Sappling-Chores/Cyprus/Assets/Edit_Gallery/Edit2.png

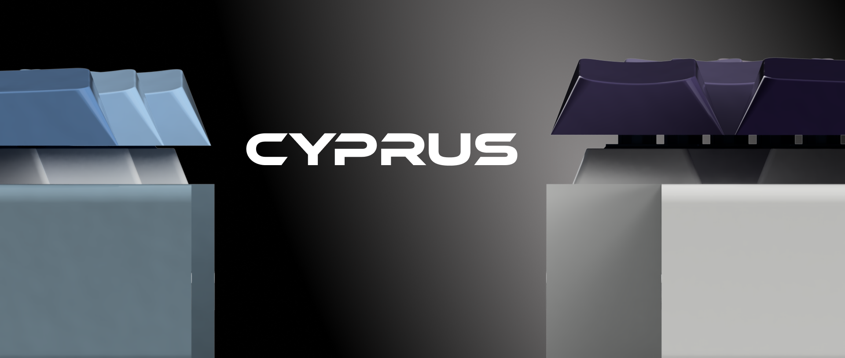
Assets/Edit_Gallery/Edit2.png
