Sappling-Chores/Cyprus/Assets/Edit_Gallery/Edit3.png

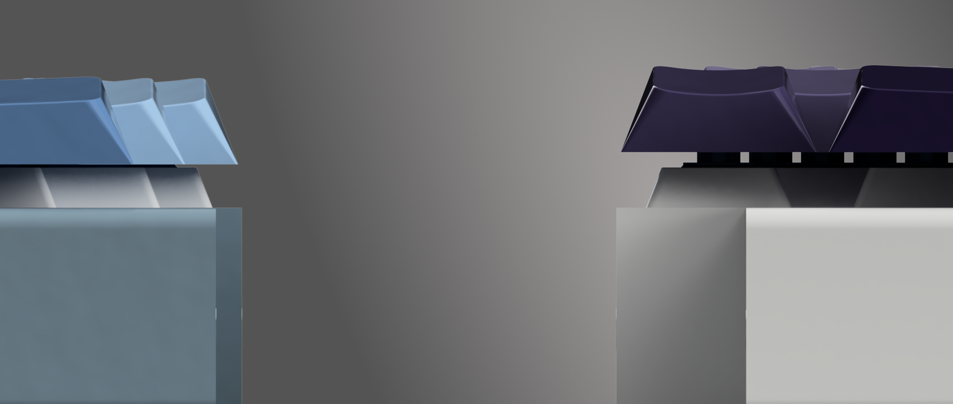
Assets/Edit_Gallery/Edit3.png
