Sappling-Chores/Cyprus/Assets/Edit_Gallery/Edit4.png

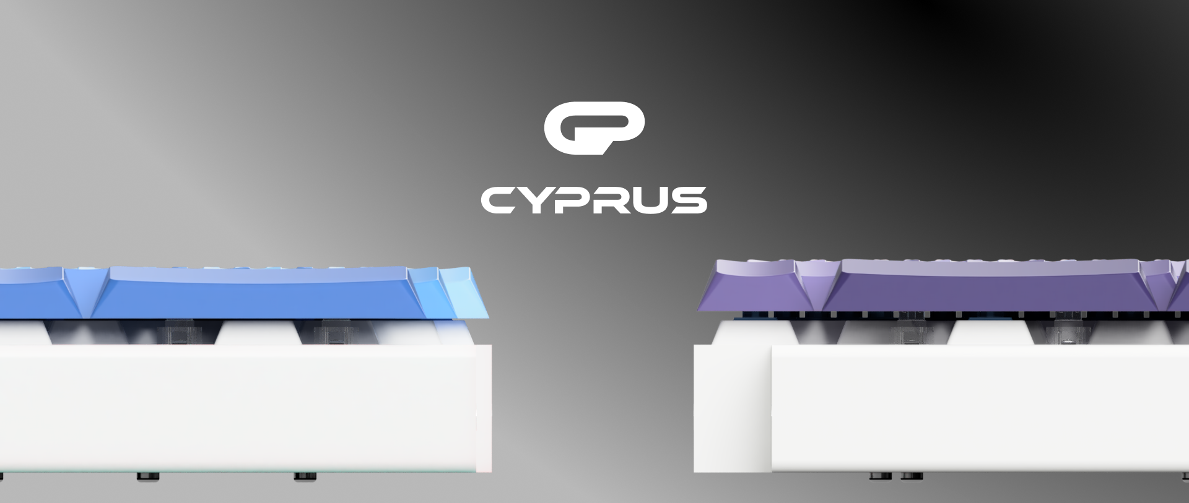
Assets/Edit_Gallery/Edit4.png
