Sappling-Chores/Cyprus/Assets/Edit_Gallery/Edit7 (2).png

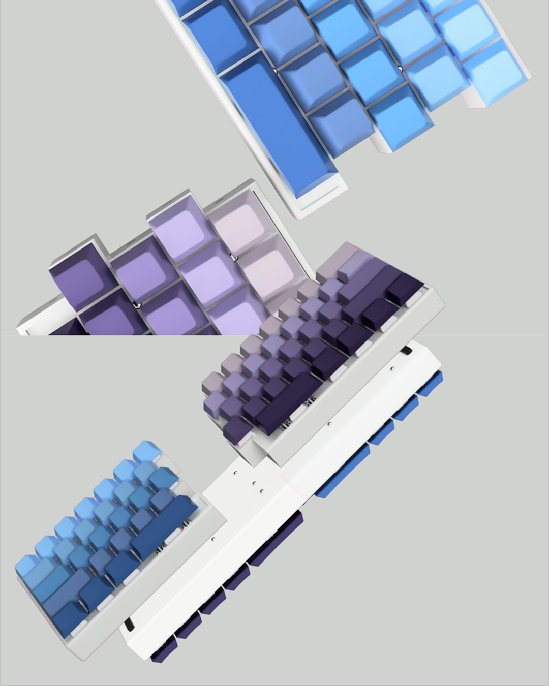
Assets/Edit_Gallery/Edit7 (2).png
