Sappling-Chores/Cyprus/Assets/Edit_Gallery/Edit9.png

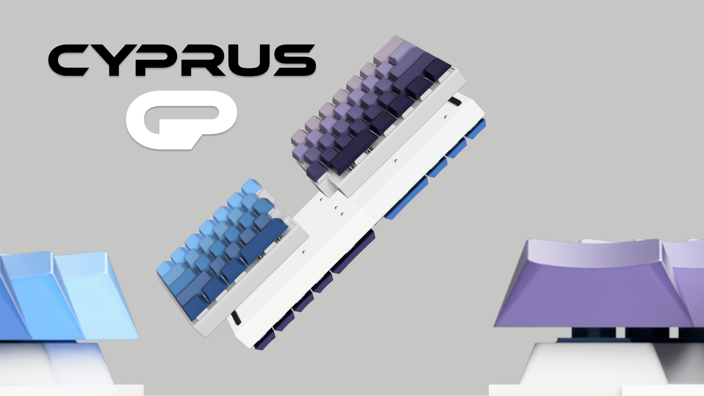
Assets/Edit_Gallery/Edit9.png
