Sappling-Chores/Cyprus/Assets/Edit_Gallery/Edit11.png

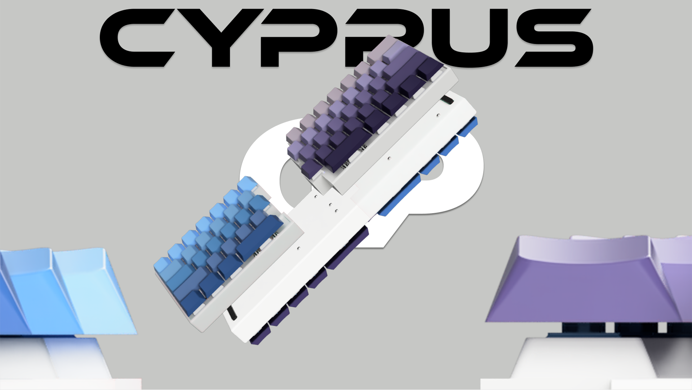
Assets/Edit_Gallery/Edit11.png
