Sappling-Chores/Cyprus/Assets/Edit_Gallery/Edit15.png

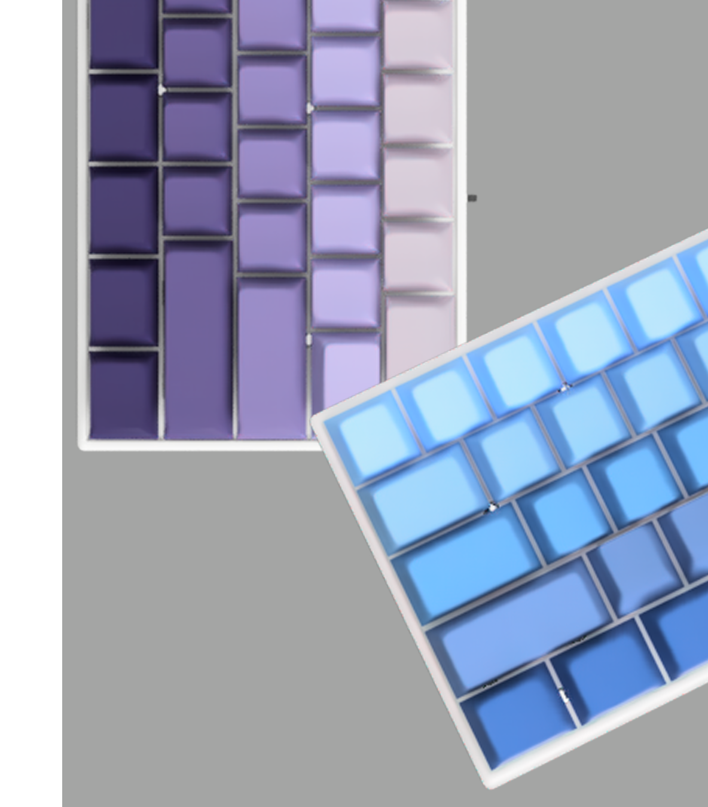
Assets/Edit_Gallery/Edit15.png
