Sappling-Chores/Cyprus/Assets/Edit_Gallery/Edit16.png

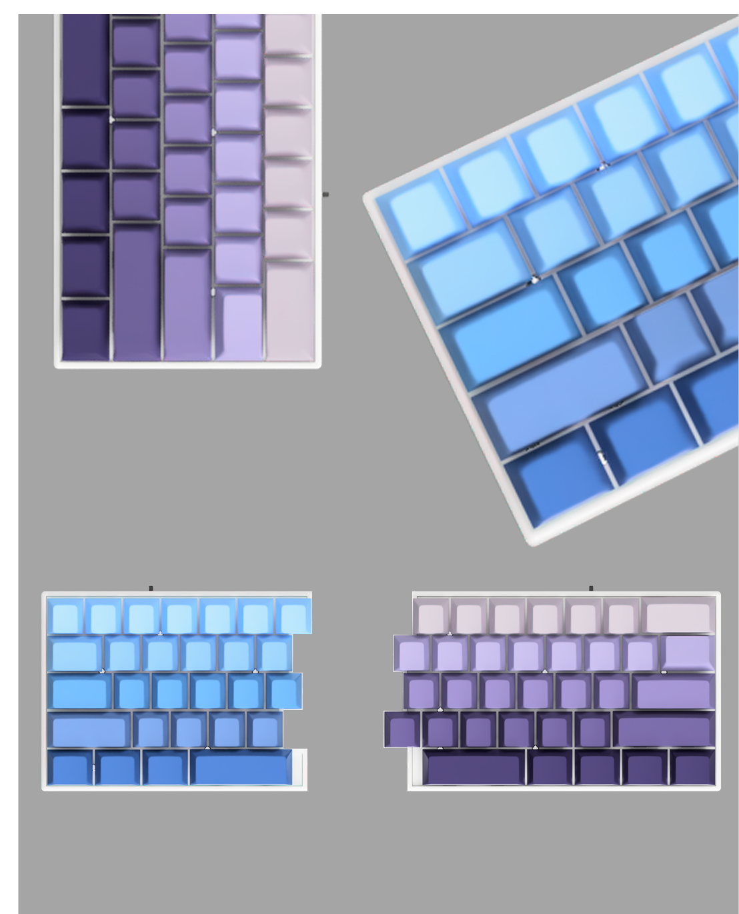
Assets/Edit_Gallery/Edit16.png
