Sappling-Chores/Cyprus/Assets/Edit_Gallery/Edit17.png

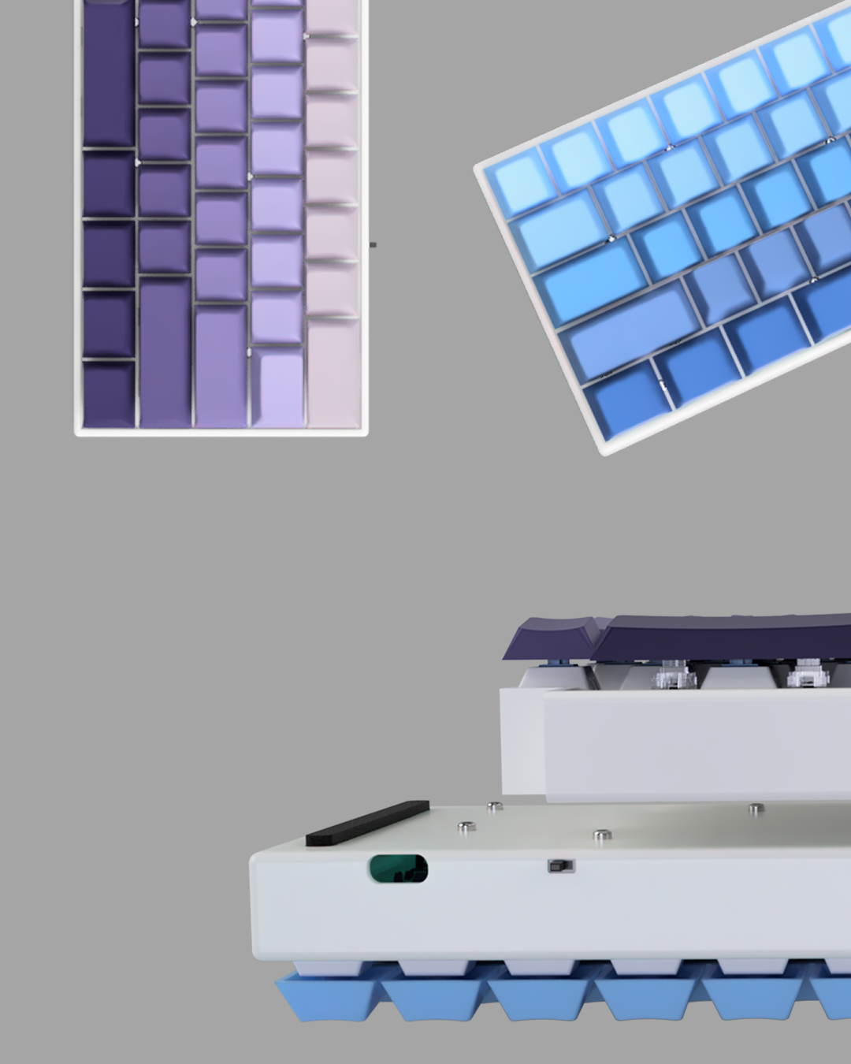
Assets/Edit_Gallery/Edit17.png
