Sappling-Chores/Cyprus/Assets/Edit_Gallery/Edit18.png

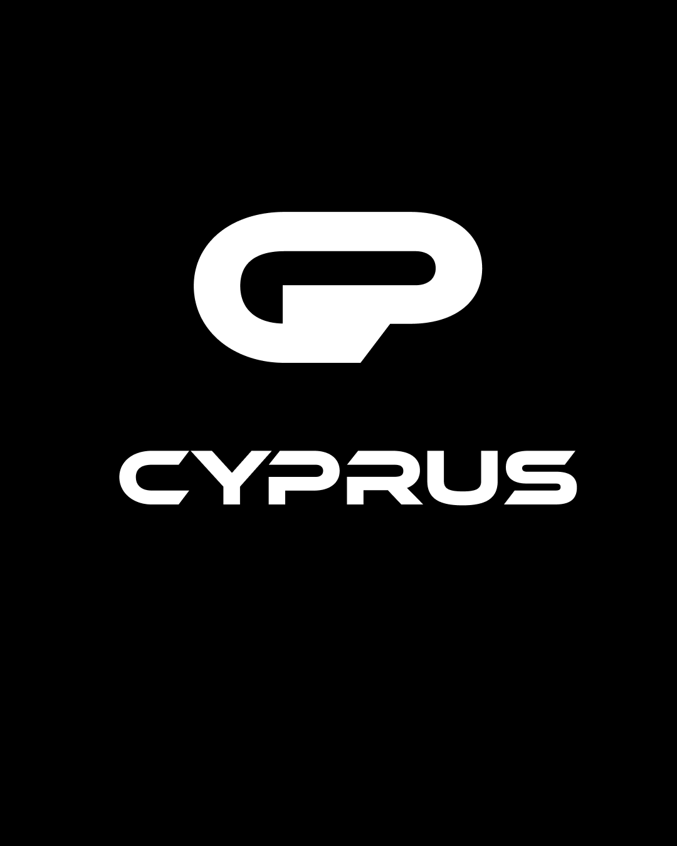
Assets/Edit_Gallery/Edit18.png
