Sappling-Chores/Cyprus/Assets/Edit_Gallery/Edit19.png

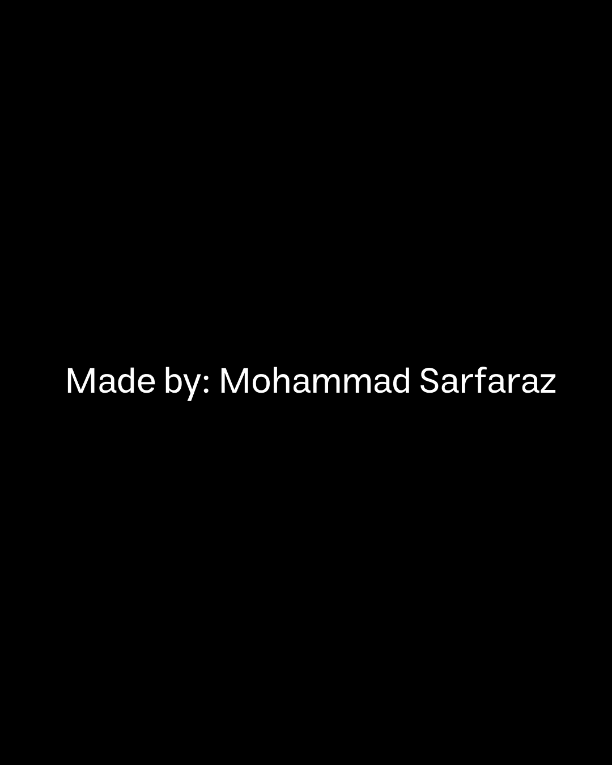
Assets/Edit_Gallery/Edit19.png
