Sappling-Chores/Cyprus/Assets/Render_Gallery/Render1.png

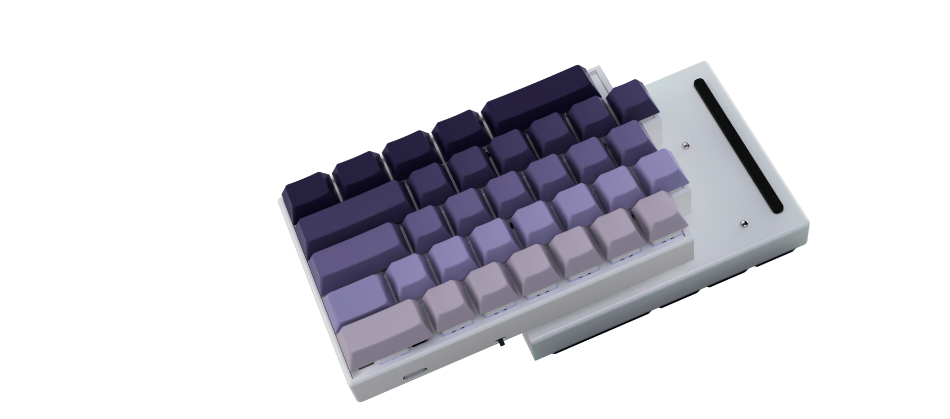
Assets/Render_Gallery/Render1.png
