Sappling-Chores/Cyprus/Assets/Render_Gallery/Render3.PNG

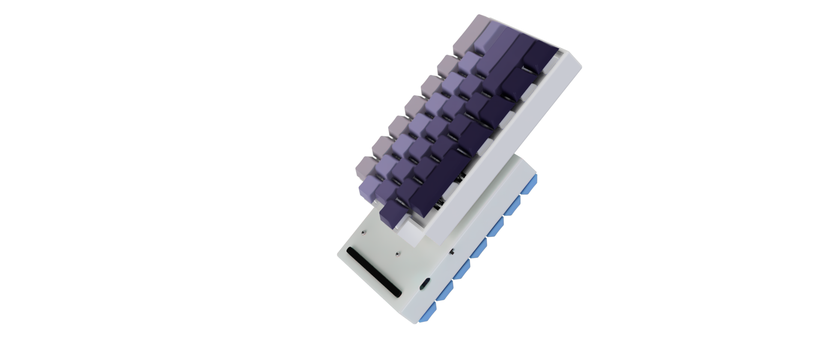
Assets/Render_Gallery/Render3.PNG
