Sappling-Chores/Cyprus/Assets/Render_Gallery/Render5.png

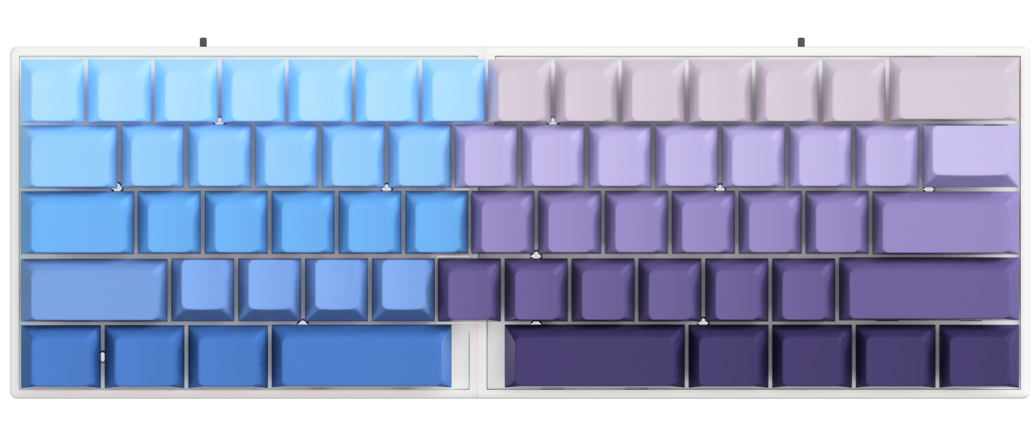
Assets/Render_Gallery/Render5.png
