Sappling-Chores/Cyprus/Assets/Render_Gallery/Render6.png

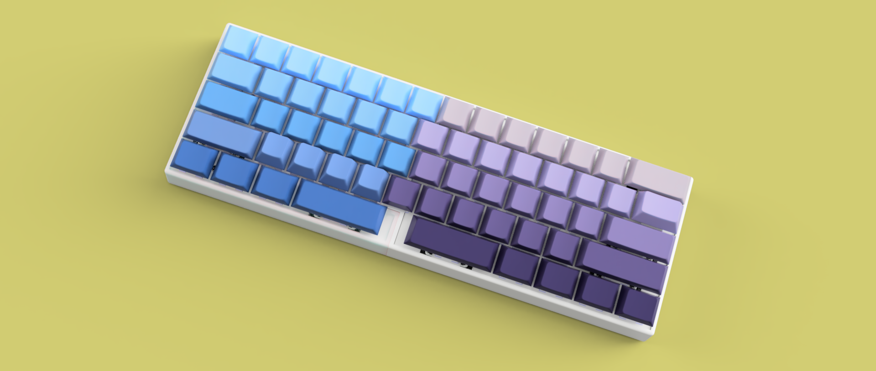
Assets/Render_Gallery/Render6.png
