Sappling-Chores/Cyprus/Assets/Render_Gallery/Render8.png

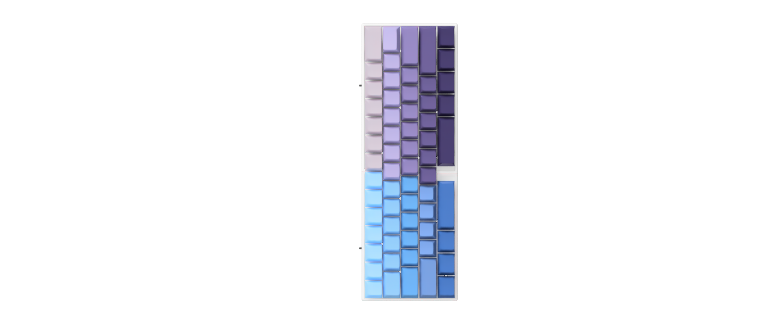
Assets/Render_Gallery/Render8.png
