Sappling-Chores/Cyprus/Assets/Render_Gallery/Render9.png

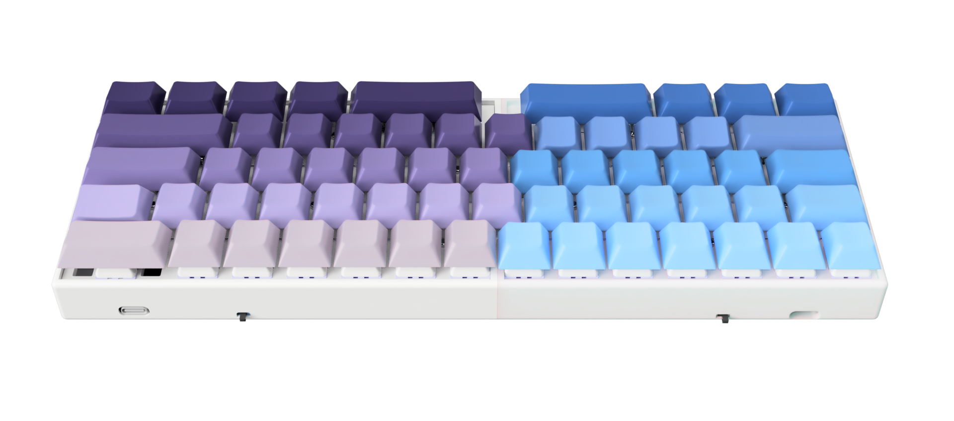
Assets/Render_Gallery/Render9.png
