Sappling-Chores/Cyprus/Assets/Render_Gallery/Render10.png

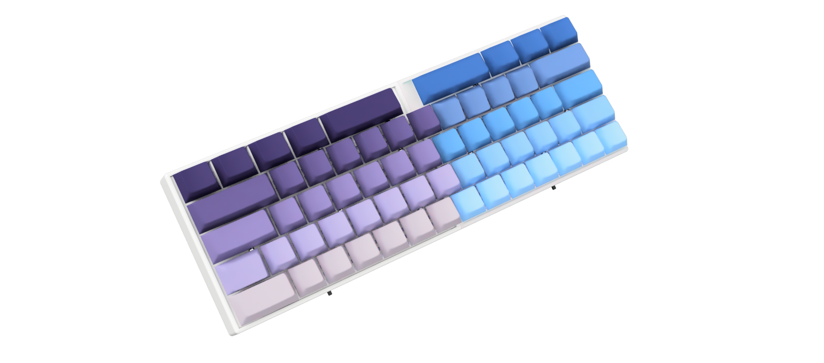
Assets/Render_Gallery/Render10.png
