Sappling-Chores/Cyprus/Assets/Render_Gallery/Render12.png

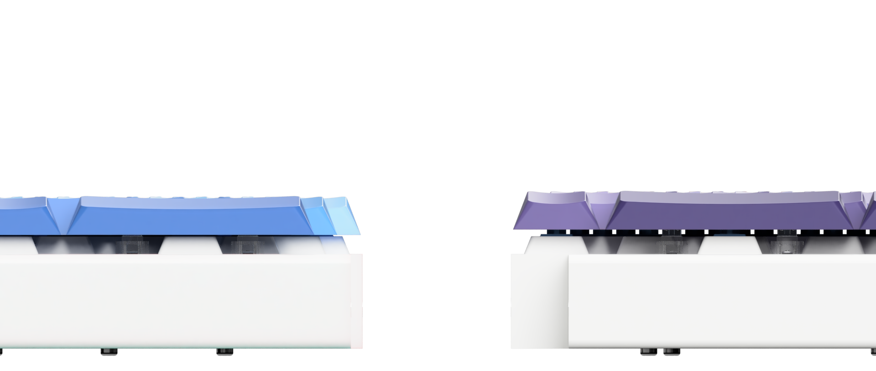
Assets/Render_Gallery/Render12.png
