Sappling-Chores/Cyprus/Assets/Render_Gallery/Render13.png

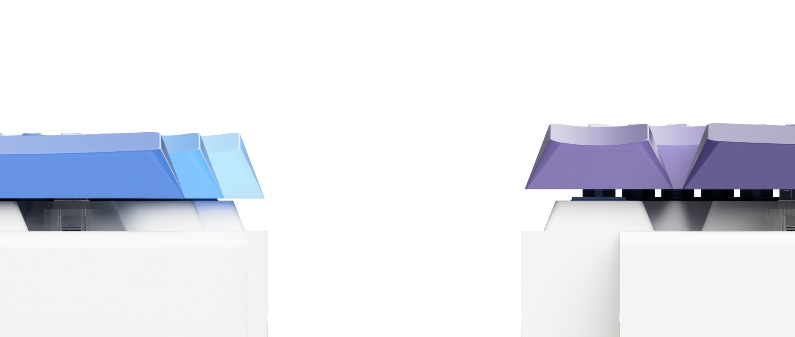
Assets/Render_Gallery/Render13.png
