Sappling-Chores/Cyprus/Assets/Render_Gallery/Render14.png

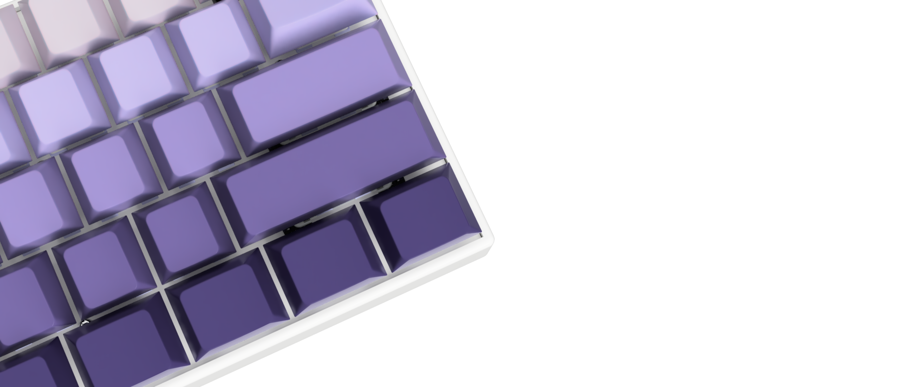
Assets/Render_Gallery/Render14.png
