Sappling-Chores/Cyprus/Assets/Render_Gallery/Render15.png

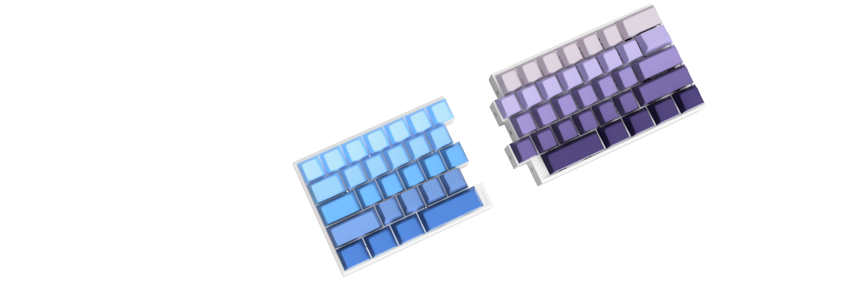
Assets/Render_Gallery/Render15.png
