Sappling-Chores/Cyprus/Assets/Render_Gallery/Render16.png

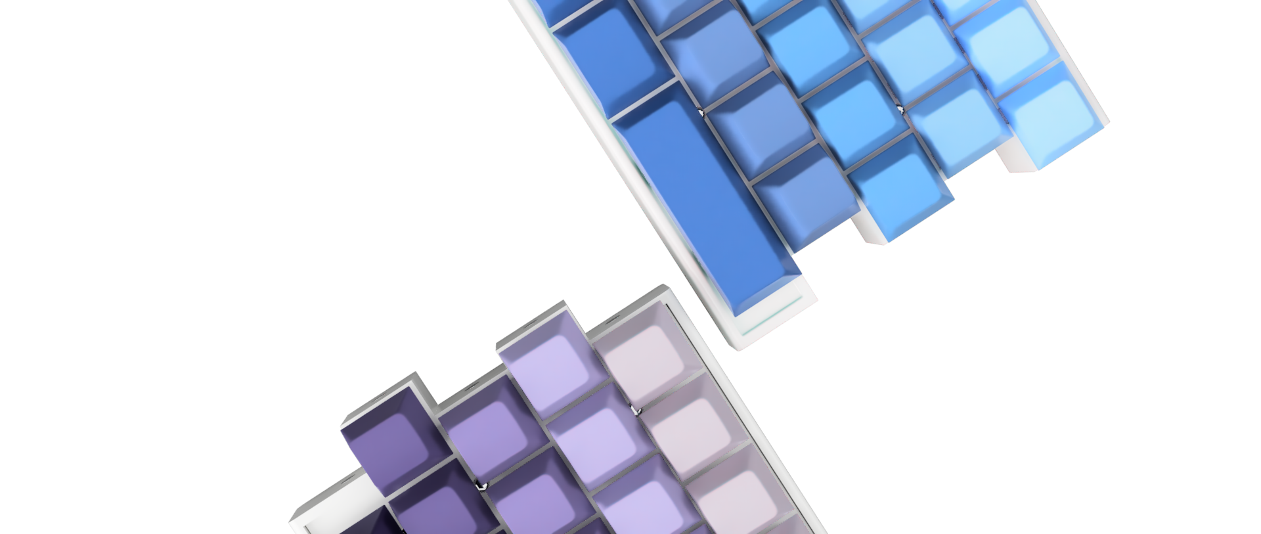
Assets/Render_Gallery/Render16.png
