Sappling-Chores/Cyprus/Assets/Render_Gallery/Render17.png

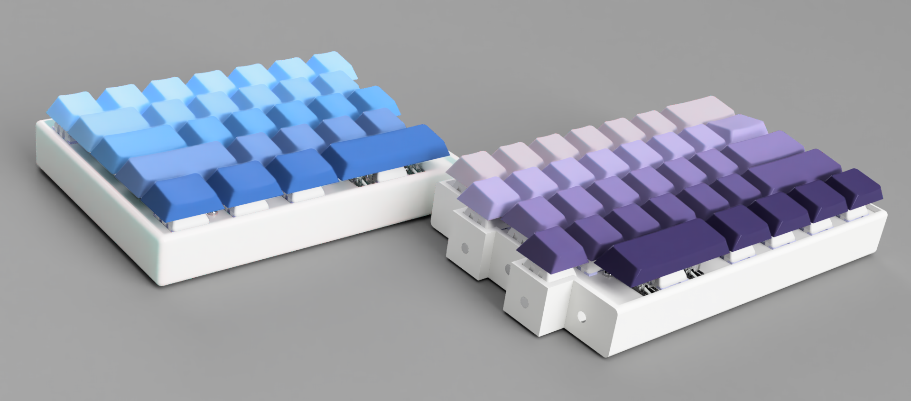
Assets/Render_Gallery/Render17.png
