Sappling-Chores/Cyprus/Assets/Render_Gallery/Render21.png

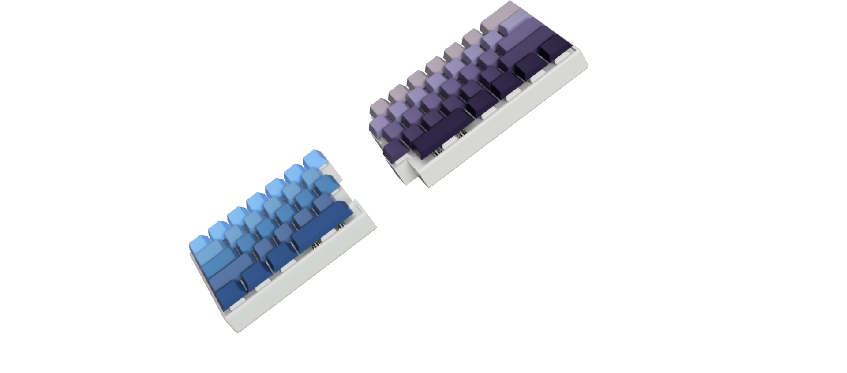
Assets/Render_Gallery/Render21.png
