Sappling-Chores/Cyprus/Assets/Render_Gallery/Render22.png

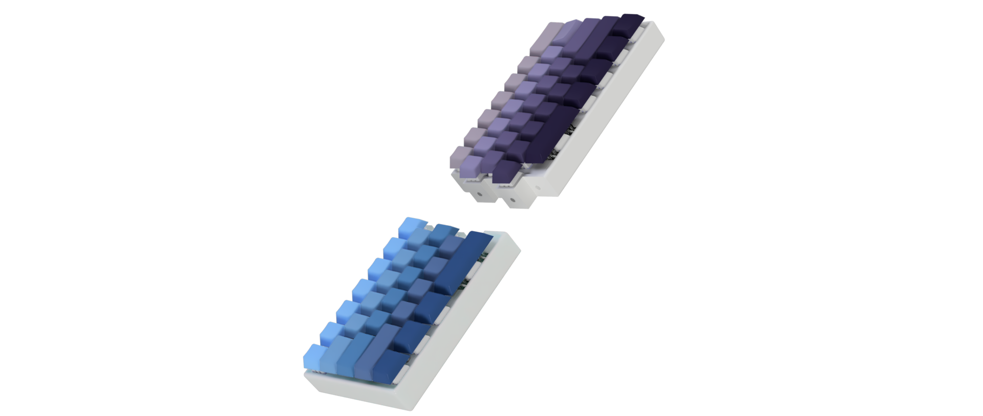
Assets/Render_Gallery/Render22.png
